PawQualityProducts/WarpCore/images/04bb8cbe3c637bdfd85d25d95b7fc5f5_preview_featured.jpg

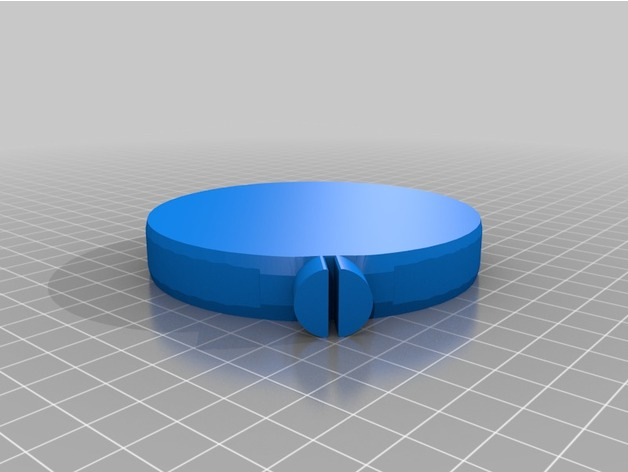
images/04bb8cbe3c637bdfd85d25d95b7fc5f5_preview_featured.jpg
