PawQualityProducts/WarpCore/images/8d2931d2200565526b0e25a2c7fd781d_preview_featured.jpg

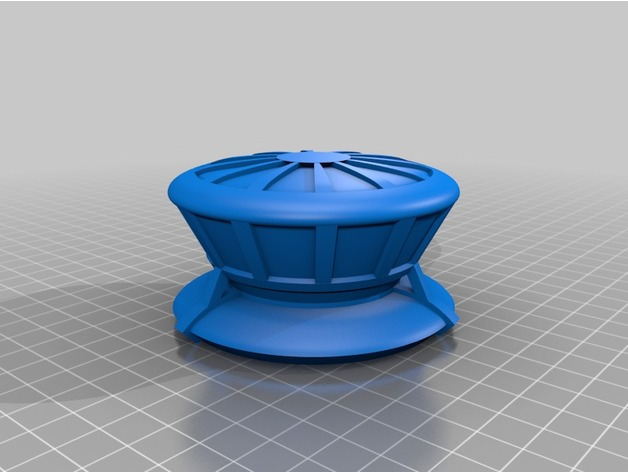
images/8d2931d2200565526b0e25a2c7fd781d_preview_featured.jpg
