PawQualityProducts/WarpCore/images/296c487f8d085d96614c041e741763c5_preview_featured.JPG

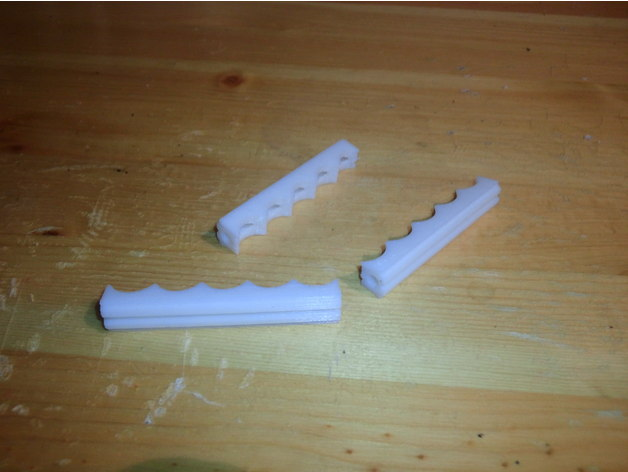
images/296c487f8d085d96614c041e741763c5_preview_featured.JPG
