PawQualityProducts/WarpCore/images/5533f7be08558061f123df7ab23d1d42_preview_featured.JPG

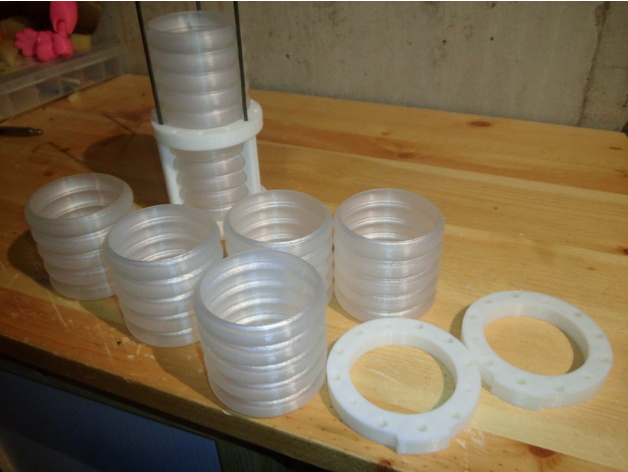
images/5533f7be08558061f123df7ab23d1d42_preview_featured.JPG
