PawQualityProducts/WarpCore/images/a7f46aaf49c289641c9b2b7bd3605679_preview_featured.jpg

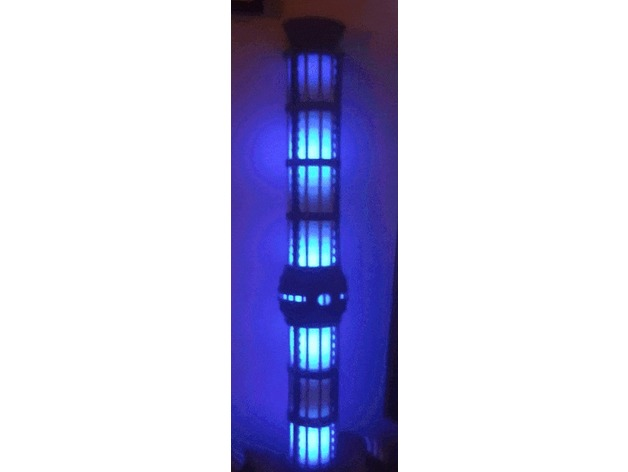
images/a7f46aaf49c289641c9b2b7bd3605679_preview_featured.jpg
