PawQualityProducts/WarpCore/images/d64cd4cd32a70dd79d2cc455c8605762_preview_featured.jpg

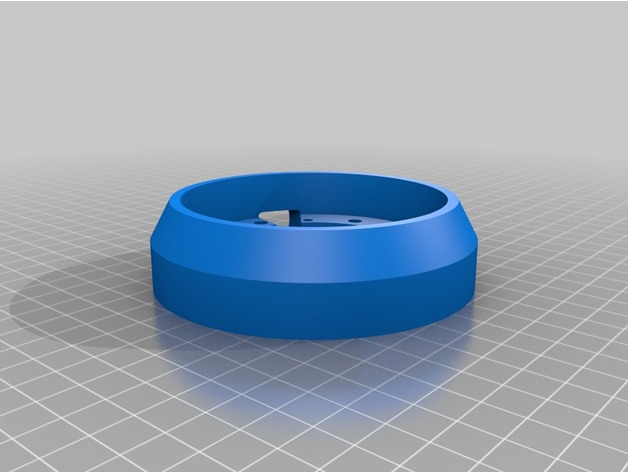
images/d64cd4cd32a70dd79d2cc455c8605762_preview_featured.jpg
