PawQualityProducts/WarpCore/images/e04d517b5e07b5c9a5233b90f2b9cb2e_preview_featured.JPG

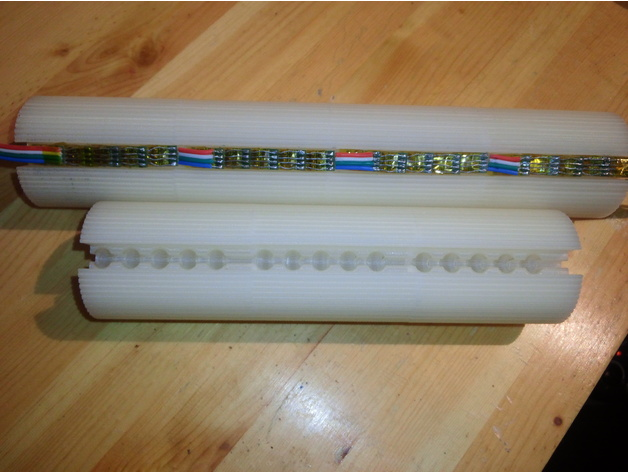
images/e04d517b5e07b5c9a5233b90f2b9cb2e_preview_featured.JPG
