PawQualityProducts/WarpCore/Cura/CE5P_diffuser_support.3mf

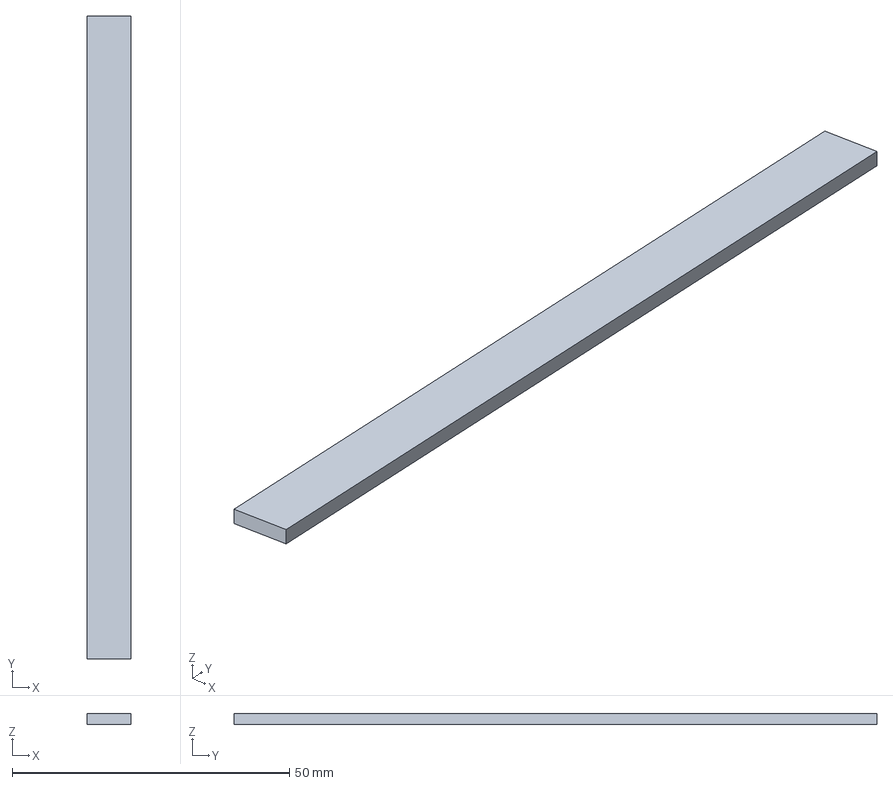
[picture p28: CAD file, 2021-07-17]
Cura/CE5P_diffuser_support.3mf
8.00 x 116.0 x 2.00 mm
