PawQualityProducts/WarpCore/files/Vertical_Tension_Member.stl

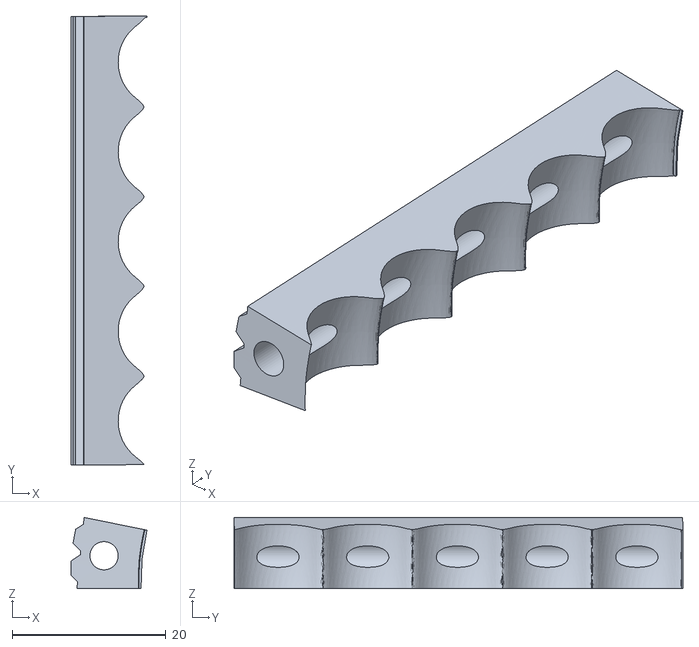
[picture p29: CAD file, 2021-07-17]
files/Vertical_Tension_Member.stl
9.89 x 58.5 x 9.26
